wcs3/GPS_CLock/kicad/3d/MAX-M8C-0-10--3DModel-STEP-56544.STEP

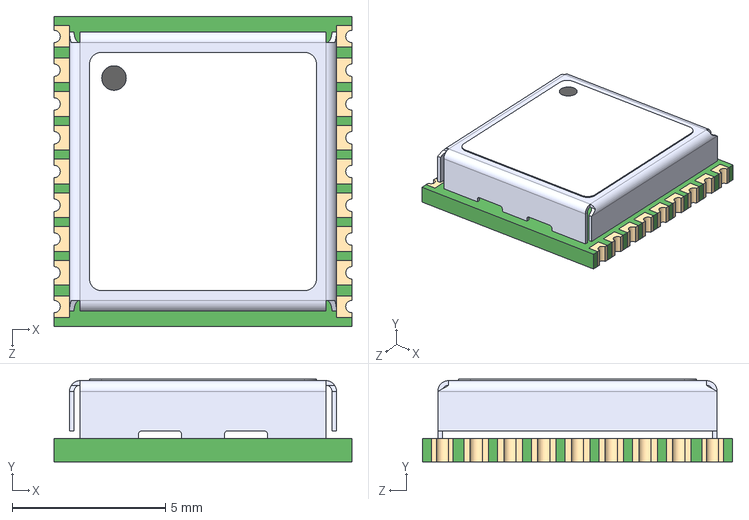
[picture p15: CAD file, 2022-12-29]
kicad/3d/MAX-M8C-0-10--3DModel-STEP-56544.STEP
9.70 x 2.70 x 10.1 mm
