wcs3/GPS_CLock/kicad/3d/ACPSX04-41.STEP

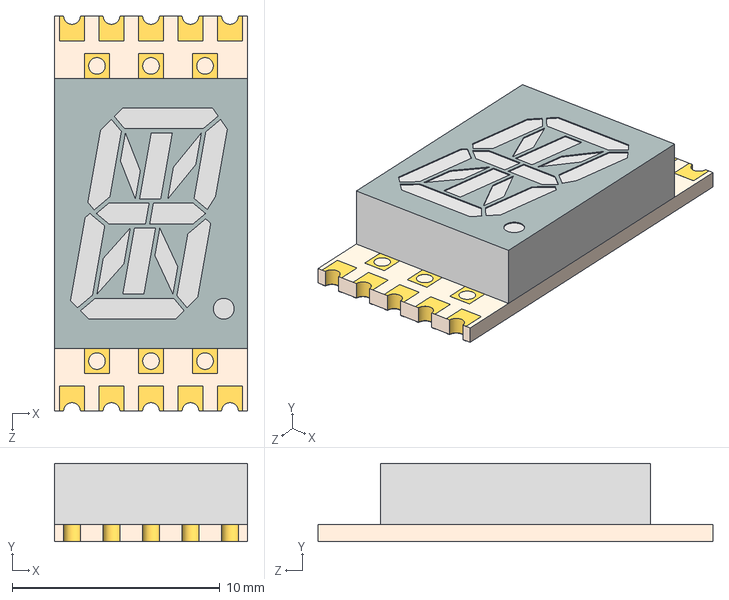
[picture p16: CAD file, 2022-12-29]
kicad/3d/ACPSX04-41.STEP
9.30 x 3.77 x 19.0 mm
