wcs3/GPS_CLock/kicad/3d/TactileSw6x6x4.3.STEP

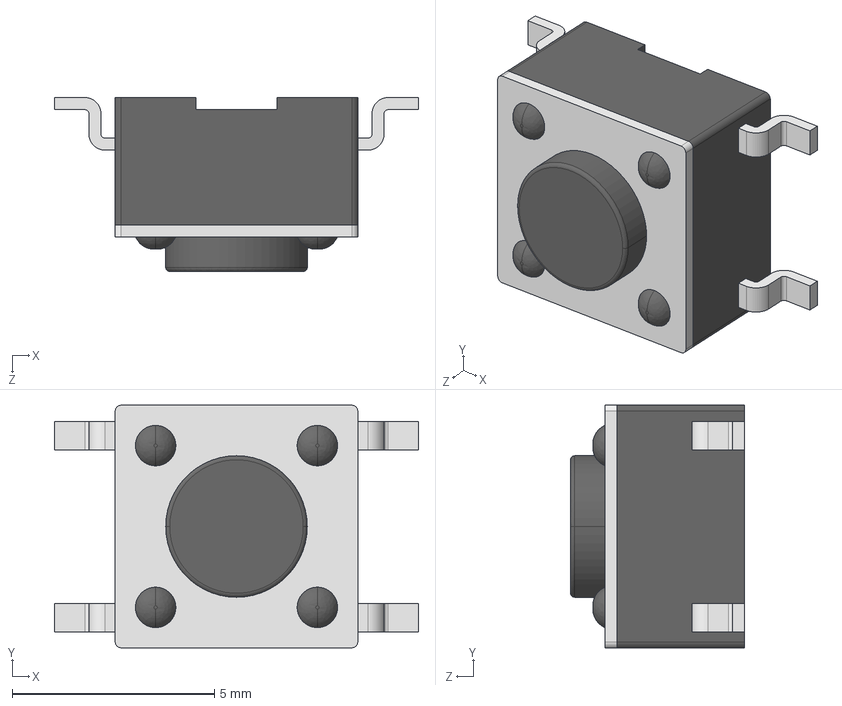
[picture p17: CAD file, 2022-12-29]
kicad/3d/TactileSw6x6x4.3.STEP
9.00 x 6.00 x 4.30 mm
