wcs3/GPS_CLock/kicad/3d/1-1734839-6.step

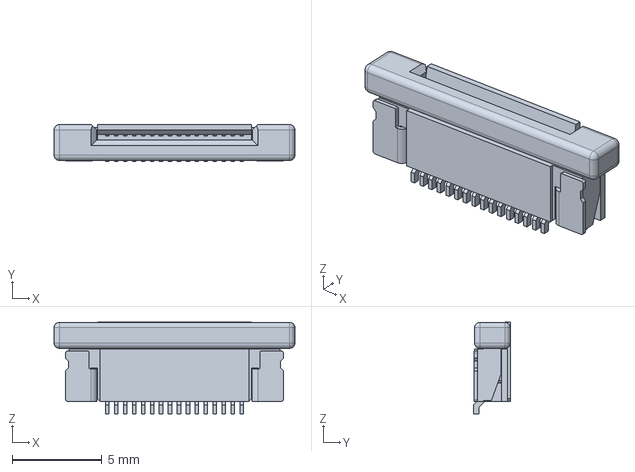
[picture p18: CAD file, 2022-12-29]
kicad/3d/1-1734839-6.step
13.4 x 2.05 x 5.11 mm
