wcs3/GPS_CLock/kicad/3d/7-Segment_0.4in_SMD.step

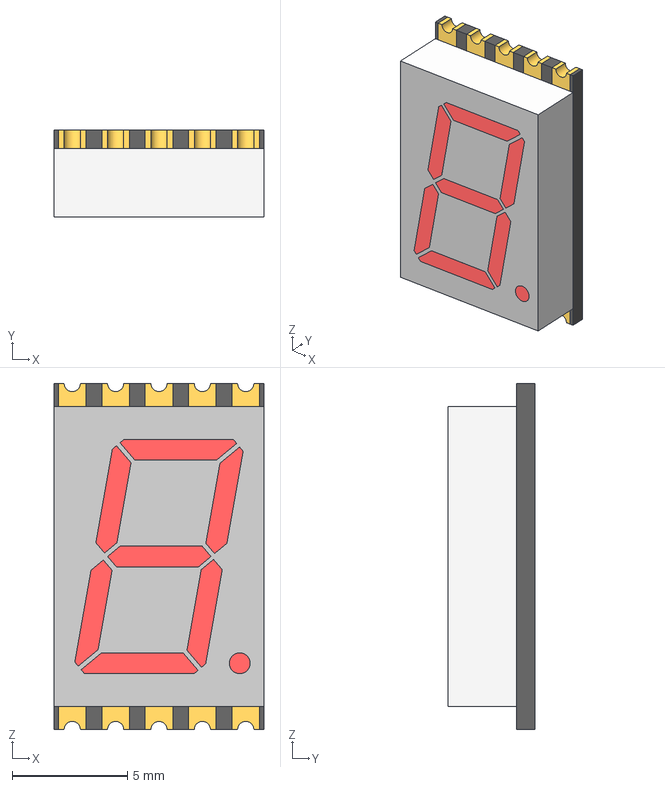
[picture p19: CAD file, 2022-12-29]
kicad/3d/7-Segment_0.4in_SMD.step
9.10 x 3.75 x 15.0 mm
dp
pcb
d
b
c
f
g
e
a
digitBlock
