wcs3/GPS_CLock/kicad/3d/FH35-21S-0.3SHW.stp

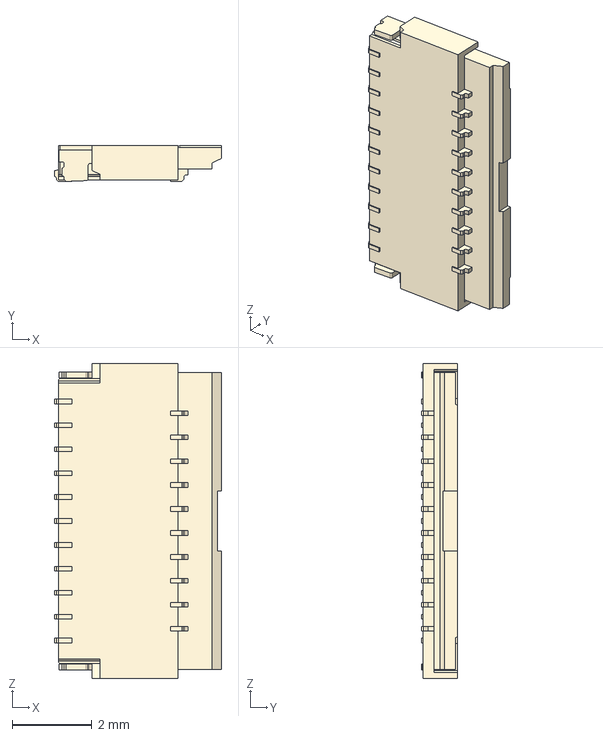
[picture p20: CAD file, 2022-12-29]
kicad/3d/FH35-21S-0.3SHW.stp
4.20 x 0.9 x 7.90 mm
