wcs3/GPS_CLock/kicad/3d/14-Segment_0.4in_SMD.step

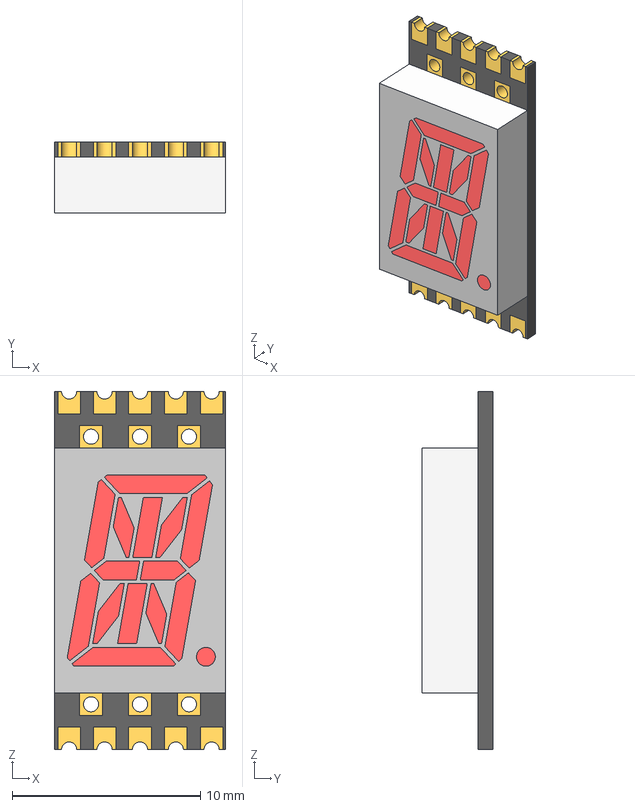
[picture p21: CAD file, 2022-12-29]
kicad/3d/14-Segment_0.4in_SMD.step
9.10 x 3.75 x 19.0 mm
k
c
l
h
a
dp
j
b
e
p
g
m
d
digitBlock
n
f
pcb
