wcs3/GPS_CLock/kicad/3d/PSON30P120X100X35-8N.step

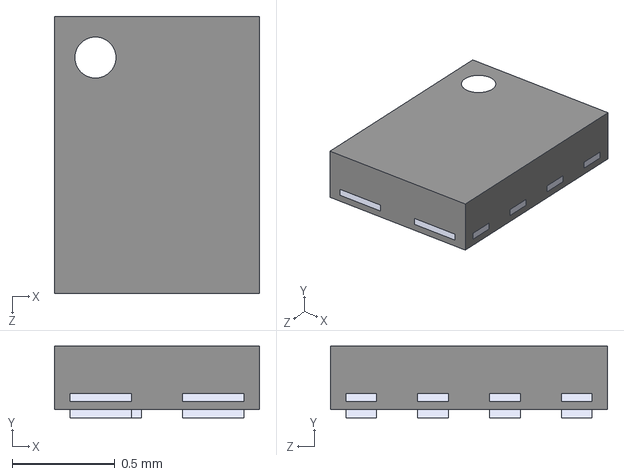
[picture p22: CAD file, 2022-12-29]
kicad/3d/PSON30P120X100X35-8N.step
1.00 x 0.35 x 1.35 mm
