wcs3/GPS_CLock/kicad/3d/ACSX08-51.STEP

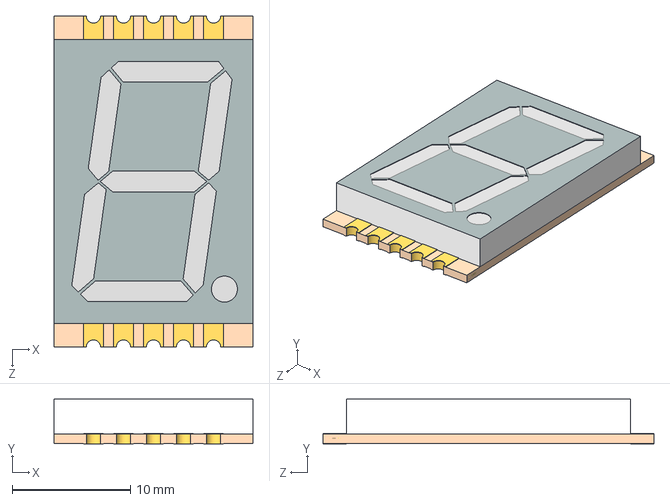
[picture p23: CAD file, 2022-12-29]
kicad/3d/ACSX08-51.STEP
16.8 x 3.80 x 28.0 mm
