wcs3/GPS_CLock/kicad/3d/EVQP4-HB3B_KB3Q_MB3K.STEP

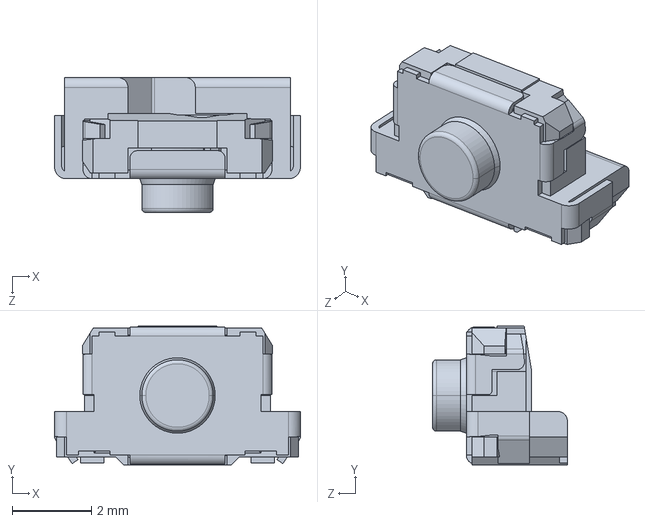
[picture p24: CAD file, 2022-12-29]
kicad/3d/EVQP4-HB3B_KB3Q_MB3K.STEP
6.20 x 3.50 x 3.40 mm
